Mliameikoo/thermal-type-printer/software/TypeWriter/Core/Inc/config.h

#ifndef __CONFIG_H
#define __CONFIG_H

/* Includes ------------------------------------------------------------------*/
#include "stm32f1xx_hal.h"
/* Private includes ----------------------------------------------------------*/
#include <stdio.h>
#include <stdbool.h>
/* Exported types ------------------------------------------------------------*/

/* Exported functions prototypes ---------------------------------------------*/

/* Private defines -----------------------------------------------------------*/
// #define ADC_RAW_DATA_DEPTH  32      // ADC采样深度
// #define ADC_CHANNEL_NUMS    1       // ADC采样通道数

#endif
/************************ (C) COPYRIGHT STMicroelectronics *****END OF FILE****/
